nevermore3d/Nevermore_Max/Fan_Scrolls/Sanyo_C70x20.stl

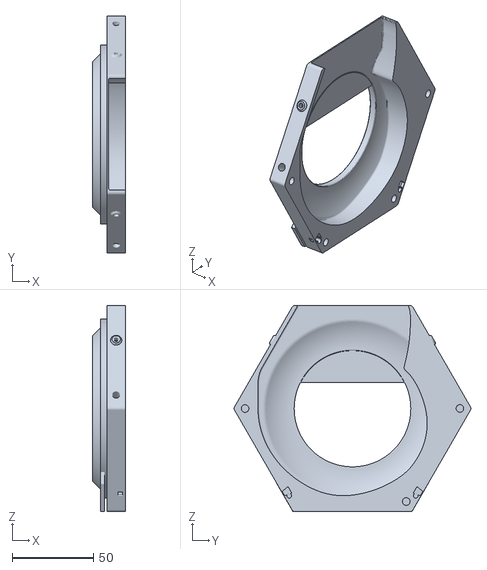
[picture p19: CAD file, 2022-08-07]
Fan_Scrolls/Sanyo_C70x20.stl
20.3 x 145.4 x 126.5
