nevermore3d/Nevermore_Max/Frame/Frame_Interconnect_1.stl

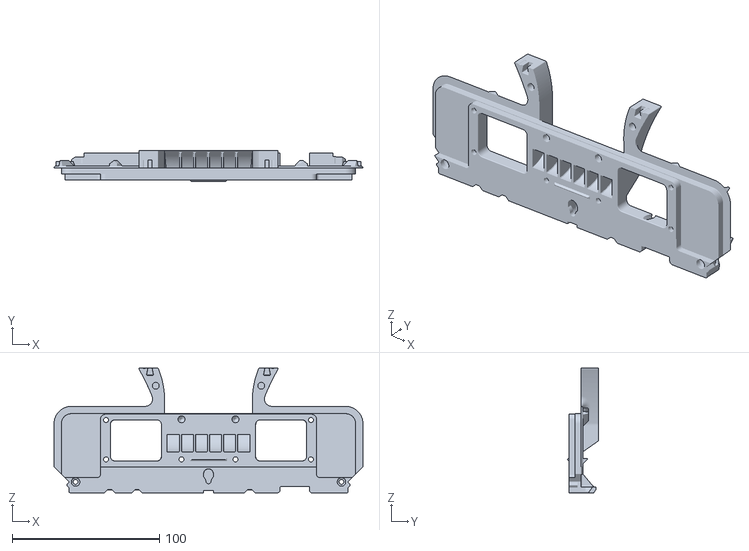
[picture p20: CAD file, 2022-08-07]
Frame/Frame_Interconnect_1.stl
209.6 x 21.1 x 84.7
