nevermore3d/Nevermore_Max/Front_Panels_Miscellaneous/Front_Panel_Twist_Latch_x2.stl

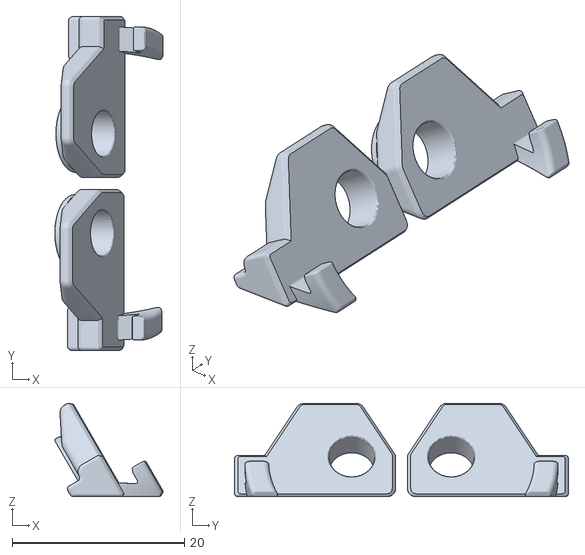
[picture p21: CAD file, 2022-08-05]
Front_Panels_Miscellaneous/Front_Panel_Twist_Latch_x2.stl
12.6 x 38.8 x 10.9
