nevermore3d/Nevermore_Max/Printed_Panels/Back_Panel_SANYO_fan.stl

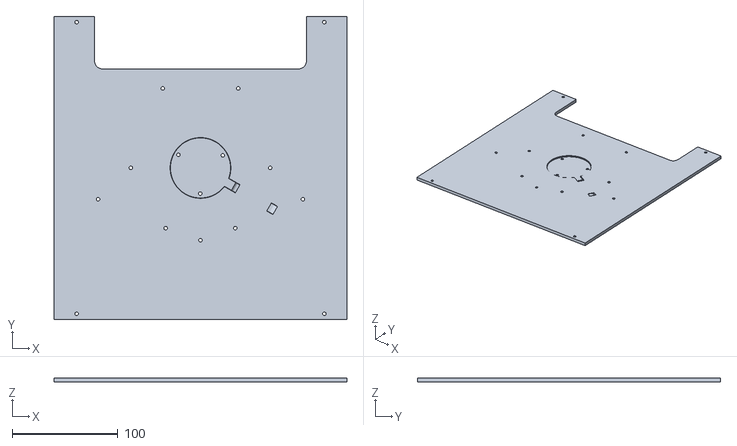
[picture p22: CAD file, 2022-09-15]
Printed_Panels/Back_Panel_SANYO_fan.stl
277.4 x 287.1 x 4.00
