nevermore3d/Nevermore_Max/Fan_Scrolls/Air_Guides_and_bottom_crosslinks.stl

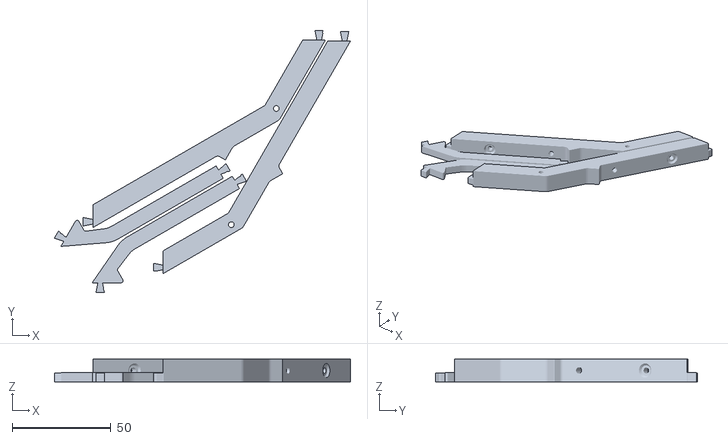
[picture p23: CAD file, 2022-08-03]
Fan_Scrolls/Air_Guides_and_bottom_crosslinks.stl
149.9 x 132.8 x 11.5
