nevermore3d/Nevermore_Max/Fan_Scrolls/High_Efficiency/Fan_Scroll _Sanyo.stl

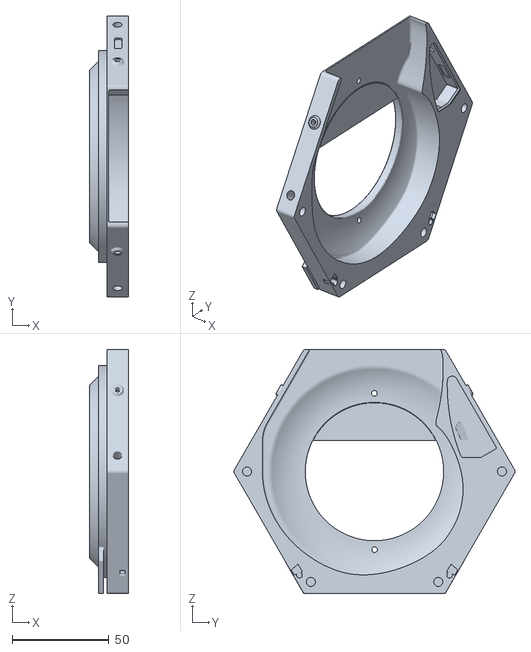
[picture p24: CAD file, 2023-03-02]
Fan_Scrolls/High_Efficiency/Fan_Scroll _Sanyo.stl
20.3 x 145.4 x 126.5
