nevermore3d/Nevermore_Max/Frame/Frame_Interconnect_3.stl

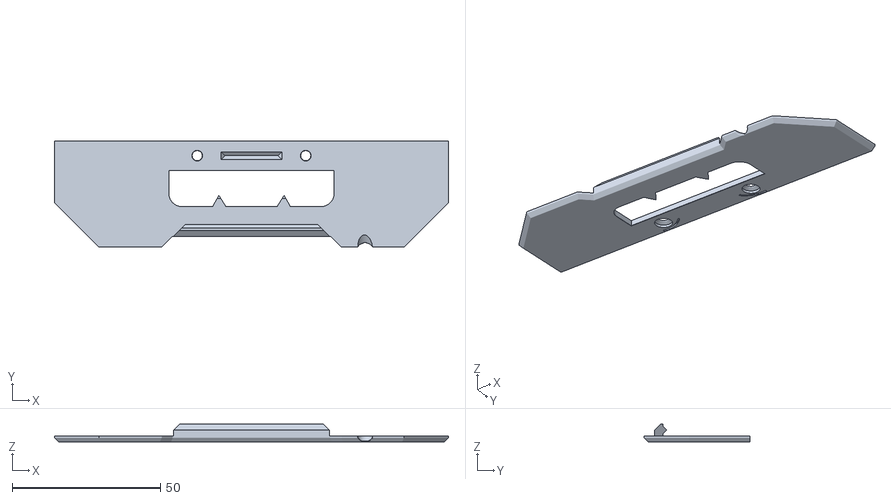
[picture p25: CAD file, 2022-08-01]
Frame/Frame_Interconnect_3.stl
133.0 x 35.9 x 6.00
