nevermore3d/Nevermore_Max/Frame/Frame_Interconnect_2.stl

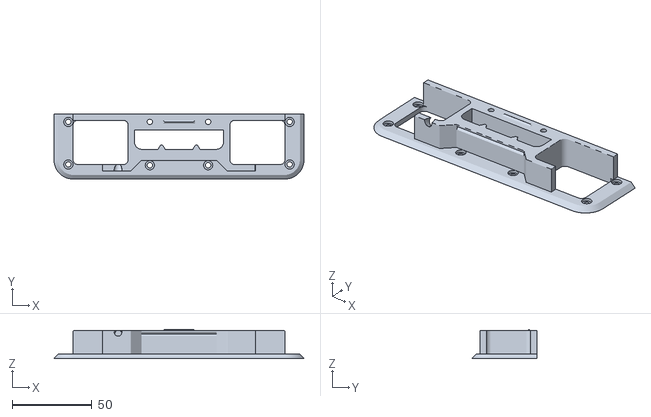
[picture p26: CAD file, 2022-08-01]
Frame/Frame_Interconnect_2.stl
157.0 x 40.9 x 18.5
