nevermore3d/Nevermore_Max/Printed_Panels/Can_You_Remove_the_Latch_Test_Print.stl

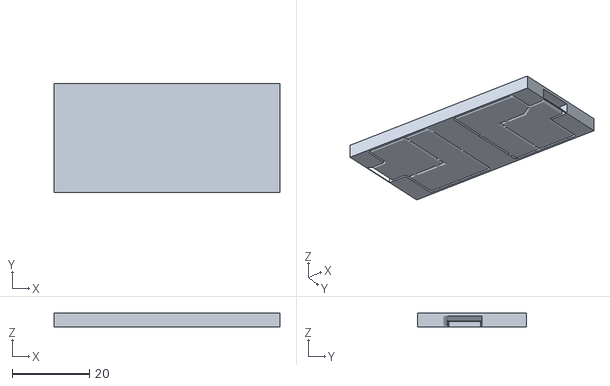
[picture p27: CAD file, 2022-08-05]
Printed_Panels/Can_You_Remove_the_Latch_Test_Print.stl
58.5 x 28.2 x 3.60
